WiddleWabbit/MQTT-ModularControllerBoard/Outputs/Models/MQTT-ModularControllerBoard-Back.png

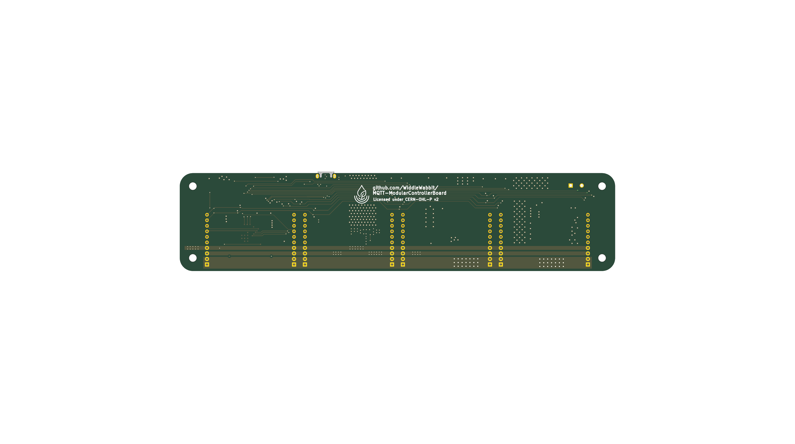
Outputs/Models/MQTT-ModularControllerBoard-Back.png
