WiddleWabbit/MQTT-ModularControllerBoard/Outputs/Models/MQTT-ModularControllerBoard-Front.png

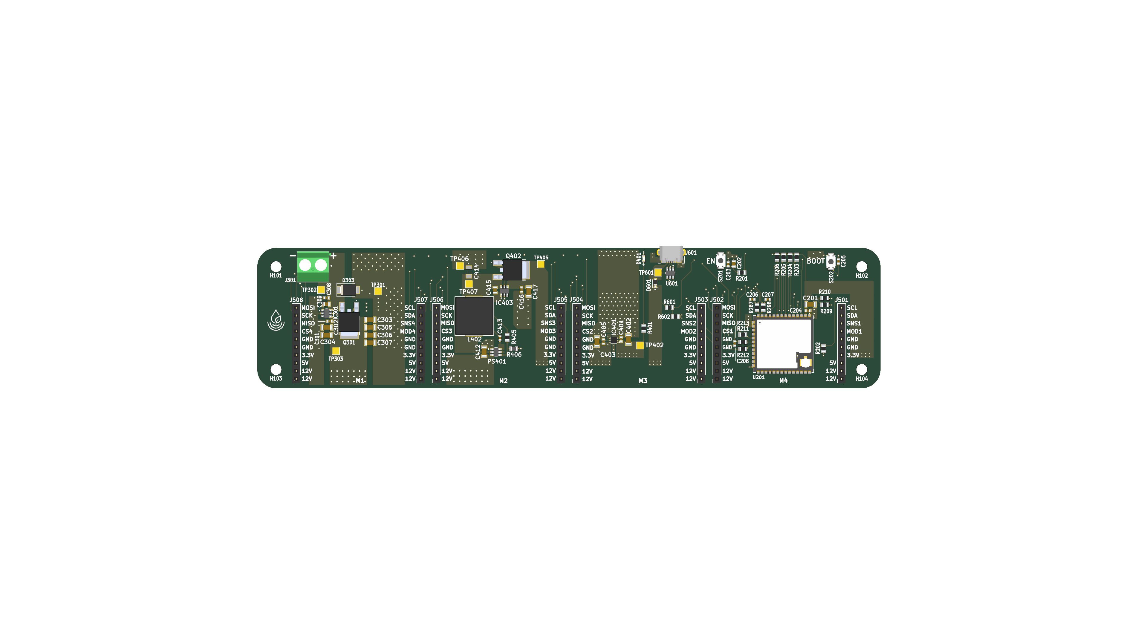
Outputs/Models/MQTT-ModularControllerBoard-Front.png
