WiddleWabbit/MQTT-ModularControllerBoard/Firmware/test/test_desktop/test_networking.cpp

#include <string>

#include <unity.h>

#include "MqttService.h"
#include "NtpService.h"
#include "WifiManager.h"
#include "fakes/FakeClock.h"
#include "fakes/FakeMqttClient.h"
#include "fakes/FakeNtpAdapter.h"
#include "fakes/FakeWifi.h"

namespace
{
FakeClock* clockForCallback = nullptr;
std::string receivedTopic;
std::string receivedPayload;

void recordMessage(const char* topic, const uint8_t* payload, size_t length,
                   void*)
{
  receivedTopic = topic == nullptr ? "" : topic;
  receivedPayload.assign(reinterpret_cast<const char*>(payload), length);
}

WifiManagerConfig wifiConfig()
{
  return {"garden", "secret", 1000, 100, 400};
}

MqttConfig mqttConfig()
{
  static const MqttSubscription subscriptions[] = {
    {"controller/command", 1},
    {"controller/config", 0},
  };
  return {"watering-controller", "user", "password", subscriptions, 2, 100, 400};
}
}

void setUp()
{
  clockForCallback = nullptr;
  receivedTopic.clear();
  receivedPayload.clear();
}

void tearDown()
{
}

void testWifiStartsConnectingAndReachesConnectedState()
{
  FakeClock clock;
  FakeWifi wifi;
  WifiManager manager(wifi, clock, wifiConfig());

  manager.begin();

  TEST_ASSERT_EQUAL(WifiManagerState::Connecting, manager.state());
  TEST_ASSERT_EQUAL(1, wifi.beginCallCount);
  TEST_ASSERT_EQUAL_STRING("garden", wifi.lastSsid.c_str());

  wifi.linkState = WifiLinkState::Connected;
  manager.update();

  TEST_ASSERT_EQUAL(WifiManagerState::Connected, manager.state());
  TEST_ASSERT_TRUE(manager.isConnected());
}

void testServicesRemainIdleUntilStarted()
{
  FakeClock clock;
  FakeWifi wifi;
  FakeNtpAdapter ntpAdapter;
  FakeMqttClient mqttClient;
  WifiManager wifiManager(wifi, clock, wifiConfig());
  NtpService ntpService(ntpAdapter, clock,
                        {"a", "b", "c", 0, 0, 100});
  MqttService mqttService(mqttClient, clock, mqttConfig());

  wifiManager.update();
  ntpService.update();
  mqttService.update(true);

  TEST_ASSERT_EQUAL(WifiManagerState::Idle, wifiManager.state());
  TEST_ASSERT_EQUAL(NtpServiceState::Idle, ntpService.state());
  TEST_ASSERT_EQUAL(MqttServiceState::Idle, mqttService.state());
  TEST_ASSERT_EQUAL(0, wifi.beginCallCount);
  TEST_ASSERT_EQUAL(0, ntpAdapter.configureCallCount);
  TEST_ASSERT_EQUAL(0, mqttClient.connectCallCount);
}

void testWifiTimeoutUsesBackoffWithoutBlocking()
{
  FakeClock clock;
  FakeWifi wifi;
  WifiManager manager(wifi, clock, wifiConfig());

  manager.begin();
  clock.advance(1000);
  manager.update();

  TEST_ASSERT_EQUAL(WifiManagerState::Backoff, manager.state());
  TEST_ASSERT_EQUAL(1, wifi.disconnectCallCount);
  TEST_ASSERT_EQUAL(1, wifi.beginCallCount);

  clock.advance(99);
  manager.update();
  TEST_ASSERT_EQUAL(1, wifi.beginCallCount);

  clock.advance(1);
  manager.update();
  TEST_ASSERT_EQUAL(WifiManagerState::Connecting, manager.state());
  TEST_ASSERT_EQUAL(2, wifi.beginCallCount);
}

void testWifiRetriesWithExponentialDelayAndCapsDelay()
{
  FakeClock clock;
  FakeWifi wifi;
  WifiManager manager(wifi, clock, wifiConfig());

  manager.begin();
  for (int attempt = 0; attempt < 3; ++attempt)
  {
    clock.advance(1000);
    manager.update();
    TEST_ASSERT_EQUAL(WifiManagerState::Backoff, manager.state());
    clock.advance(attempt == 0 ? 100 : (attempt == 1 ? 200 : 400));
    manager.update();
  }

  TEST_ASSERT_EQUAL(4, wifi.beginCallCount);
  TEST_ASSERT_EQUAL(400, manager.currentRetryDelayMs());
}

void testWifiReturnsToBackoffWhenConnectedLinkIsLost()
{
  FakeClock clock;
  FakeWifi wifi;
  WifiManager manager(wifi, clock, wifiConfig());

  manager.begin();
  wifi.linkState = WifiLinkState::Connected;
  manager.update();
  wifi.linkState = WifiLinkState::Disconnected;
  manager.update();

  TEST_ASSERT_EQUAL(WifiManagerState::Backoff, manager.state());
  TEST_ASSERT_FALSE(manager.isConnected());
}

void testWifiUsesStatusSequenceAndHandlesClockWraparound()
{
  FakeClock clock;
  clock.set(UINT32_MAX - 50U);
  FakeWifi wifi;
  wifi.statusSequence = {
    WifiLinkState::Connecting,
    WifiLinkState::Connected,
  };
  WifiManager manager(wifi, clock, wifiConfig());

  manager.begin();
  clock.advance(1000);
  manager.update();

  TEST_ASSERT_EQUAL(WifiManagerState::Backoff, manager.state());
  TEST_ASSERT_EQUAL(1, wifi.disconnectCallCount);

  clock.advance(101);
  manager.update();
  TEST_ASSERT_EQUAL(WifiManagerState::Connecting, manager.state());
  TEST_ASSERT_EQUAL(2, wifi.beginCallCount);

  manager.update();
  TEST_ASSERT_EQUAL(WifiManagerState::Connected, manager.state());
}

void testNtpConfiguresAdapterAndTransitionsWhenTimeIsValid()
{
  FakeClock clock;
  FakeNtpAdapter adapter;
  NtpService service(adapter, clock,
                     {"pool.ntp.org", "time.nist.gov", nullptr, 28800, 0, 500});

  service.begin();
  TEST_ASSERT_EQUAL(NtpServiceState::WaitingForSync, service.state());
  TEST_ASSERT_FALSE(service.isSynchronized());
  TEST_ASSERT_EQUAL((time_t)0, service.currentTime());
  TEST_ASSERT_EQUAL(1, adapter.configureCallCount);
  TEST_ASSERT_EQUAL(28800, adapter.lastUtcOffsetSeconds);

  service.update();
  TEST_ASSERT_EQUAL(NtpServiceState::WaitingForSync, service.state());

  adapter.synchronized = true;
  adapter.epoch = 1700000000;
  service.update();
  TEST_ASSERT_EQUAL(NtpServiceState::Synchronized, service.state());
  TEST_ASSERT_EQUAL((time_t)1700000000, service.currentTime());
}

void testNtpRetriesConfigurationAfterSyncWaitInterval()
{
  FakeClock clock;
  FakeNtpAdapter adapter;
  NtpService service(adapter, clock,
                     {"a", "b", "c", 0, 3600, 500});

  service.begin();
  clock.advance(499);
  service.update();
  TEST_ASSERT_EQUAL(1, adapter.configureCallCount);

  clock.advance(1);
  service.update();
  TEST_ASSERT_EQUAL(2, adapter.configureCallCount);
}

void testNtpReturnsToWaitingWhenSynchronizationIsLost()
{
  FakeClock clock;
  FakeNtpAdapter adapter;
  NtpService service(adapter, clock,
                     {"a", "b", "c", 0, 0, 100});

  service.begin();
  adapter.synchronized = true;
  adapter.epoch = 1700000001;
  service.update();
  TEST_ASSERT_EQUAL(NtpServiceState::Synchronized, service.state());

  adapter.synchronized = false;
  service.update();
  TEST_ASSERT_EQUAL(NtpServiceState::WaitingForSync, service.state());
  TEST_ASSERT_EQUAL((time_t)0, service.currentTime());

  clock.advance(100);
  service.update();
  TEST_ASSERT_EQUAL(2, adapter.configureCallCount);
}

void testMqttWaitsForNetworkThenConnectsAndSubscribes()
{
  FakeClock clock;
  FakeMqttClient client;
  MqttService service(client, clock, mqttConfig());

  service.setBroker("broker.local", 1883);
  service.begin();
  service.update(false);
  TEST_ASSERT_EQUAL(MqttServiceState::WaitingForNetwork, service.state());
  TEST_ASSERT_EQUAL(0, client.connectCallCount);

  service.update(true);
  TEST_ASSERT_EQUAL(MqttServiceState::Connected, service.state());
  TEST_ASSERT_EQUAL(1, client.connectCallCount);
  TEST_ASSERT_EQUAL(2, client.subscribeCallCount);
  TEST_ASSERT_EQUAL_STRING("controller/command",
                           client.subscribedTopics[0].c_str());
}

void testMqttFailedConnectionUsesNonblockingBackoff()
{
  FakeClock clock;
  FakeMqttClient client;
  client.connectResult = false;
  MqttService service(client, clock, mqttConfig());

  service.setBroker("broker.local", 1883);
  service.begin();
  service.update(true);
  TEST_ASSERT_EQUAL(MqttServiceState::Backoff, service.state());
  TEST_ASSERT_EQUAL(1, client.connectCallCount);

  clock.advance(99);
  service.update(true);
  TEST_ASSERT_EQUAL(1, client.connectCallCount);

  clock.advance(1);
  service.update(true);
  TEST_ASSERT_EQUAL(2, client.connectCallCount);
}

void testMqttServicesLoopAndPublishesOnlyWhenConnected()
{
  FakeClock clock;
  FakeMqttClient client;
  MqttService service(client, clock, mqttConfig());

  service.setBroker("broker.local", 1883);
  service.begin();
  TEST_ASSERT_FALSE(service.publish("status", "offline", false));
  service.update(true);
  TEST_ASSERT_TRUE(service.publish("status", "online", true));
  service.update(true);

  TEST_ASSERT_EQUAL(1, client.publishCallCount);
  TEST_ASSERT_EQUAL_STRING("online", client.publishedMessages[0].payload.c_str());
  TEST_ASSERT_EQUAL(1, client.loopCallCount);
}

void testMqttForwardsInboundMessagesToApplicationHandler()
{
  FakeClock clock;
  FakeMqttClient client;
  MqttService service(client, clock, mqttConfig());

  service.setMessageHandler(recordMessage, nullptr);
  service.setBroker("broker.local", 1883);
  service.begin();
  service.update(true);
  client.deliver("controller/command", "water-now");

  TEST_ASSERT_EQUAL_STRING("controller/command", receivedTopic.c_str());
  TEST_ASSERT_EQUAL_STRING("water-now", receivedPayload.c_str());
}

void testMqttDisconnectsWhenNetworkIsLost()
{
  FakeClock clock;
  FakeMqttClient client;
  MqttService service(client, clock, mqttConfig());

  service.setBroker("broker.local", 1883);
  service.begin();
  service.update(true);
  service.update(false);

  TEST_ASSERT_EQUAL(MqttServiceState::WaitingForNetwork, service.state());
  TEST_ASSERT_EQUAL(1, client.disconnectCallCount);
}

void testMqttRetriesAfterBrokerDisconnectUsingBackoff()
{
  FakeClock clock;
  FakeMqttClient client;
  MqttService service(client, clock, mqttConfig());

  service.setBroker("broker.local", 1883);
  service.begin();
  service.update(true);
  TEST_ASSERT_EQUAL(MqttServiceState::Connected, service.state());

  client.connectedState = false;
  service.update(true);
  TEST_ASSERT_EQUAL(MqttServiceState::Backoff, service.state());

  clock.advance(99);
  service.update(true);
  TEST_ASSERT_EQUAL(1, client.connectCallCount);

  clock.advance(1);
  service.update(true);
  TEST_ASSERT_EQUAL(2, client.connectCallCount);
  TEST_ASSERT_EQUAL(MqttServiceState::Connected, service.state());
}

void testMqttReportsPublicationFailure()
{
  FakeClock clock;
  FakeMqttClient client;
  client.publishResult = false;
  MqttService service(client, clock, mqttConfig());

  service.setBroker("broker.local", 1883);
  service.begin();
  service.update(true);

  TEST_ASSERT_FALSE(service.publish("status", "online", false));
  TEST_ASSERT_EQUAL(1, client.publishCallCount);
}

void testMqttBacksOffWhenSubscriptionFails()
{
  FakeClock clock;
  FakeMqttClient client;
  client.subscribeResults = {true, false};
  MqttService service(client, clock, mqttConfig());

  service.setBroker("broker.local", 1883);
  service.begin();
  service.update(true);

  TEST_ASSERT_EQUAL(MqttServiceState::Backoff, service.state());
  TEST_ASSERT_EQUAL(1, client.disconnectCallCount);
  TEST_ASSERT_FALSE(service.publish("status", "online", false));
}

void testWifiAndMqttComposeThroughInterfaces()
{
  FakeClock clock;
  FakeWifi wifi;
  FakeMqttClient client;
  WifiManager manager(wifi, clock, wifiConfig());
  MqttService mqtt(client, clock, mqttConfig());

  manager.begin();
  mqtt.setBroker("broker.local", 1883);
  mqtt.begin();
  mqtt.update(manager.isConnected());
  TEST_ASSERT_EQUAL(0, client.connectCallCount);

  wifi.linkState = WifiLinkState::Connected;
  manager.update();
  mqtt.update(manager.isConnected());

  TEST_ASSERT_EQUAL(1, client.connectCallCount);
  TEST_ASSERT_EQUAL(MqttServiceState::Connected, mqtt.state());
}

void testMqttWithoutBrokerStaysUnconfigured()
{
  FakeClock clock;
  FakeMqttClient client;
  MqttService service(client, clock, mqttConfig());

  service.setBroker("", 1883);
  service.begin();
  service.update(true);
  service.update(true);

  TEST_ASSERT_EQUAL(MqttServiceState::Unconfigured, service.state());
  TEST_ASSERT_EQUAL(0, client.connectCallCount);

  service.setBroker(nullptr, 1883);
  service.update(true);
  TEST_ASSERT_EQUAL(0, client.connectCallCount);

  service.setBroker("broker.local", 1883);
  service.begin();
  service.update(true);

  TEST_ASSERT_EQUAL(1, client.connectCallCount);
  TEST_ASSERT_EQUAL(MqttServiceState::Connected, service.state());
}


// ========== Runner ==========

/**
 * Registers the Wi-Fi, NTP, and MQTT service cases.
 *
 * @return Nothing.
 */
void runNetworkingTests()
{
  // UNITY_BEGIN records test_main.cpp, so name this file for the report.
  UnitySetTestFile(__FILE__);
  RUN_TEST(testWifiStartsConnectingAndReachesConnectedState);
  RUN_TEST(testServicesRemainIdleUntilStarted);
  RUN_TEST(testWifiTimeoutUsesBackoffWithoutBlocking);
  RUN_TEST(testWifiRetriesWithExponentialDelayAndCapsDelay);
  RUN_TEST(testWifiReturnsToBackoffWhenConnectedLinkIsLost);
  RUN_TEST(testWifiUsesStatusSequenceAndHandlesClockWraparound);
  RUN_TEST(testNtpConfiguresAdapterAndTransitionsWhenTimeIsValid);
  RUN_TEST(testNtpRetriesConfigurationAfterSyncWaitInterval);
  RUN_TEST(testNtpReturnsToWaitingWhenSynchronizationIsLost);
  RUN_TEST(testMqttWaitsForNetworkThenConnectsAndSubscribes);
  RUN_TEST(testMqttFailedConnectionUsesNonblockingBackoff);
  RUN_TEST(testMqttServicesLoopAndPublishesOnlyWhenConnected);
  RUN_TEST(testMqttForwardsInboundMessagesToApplicationHandler);
  RUN_TEST(testMqttDisconnectsWhenNetworkIsLost);
  RUN_TEST(testMqttRetriesAfterBrokerDisconnectUsingBackoff);
  RUN_TEST(testMqttReportsPublicationFailure);
  RUN_TEST(testMqttBacksOffWhenSubscriptionFails);
  RUN_TEST(testWifiAndMqttComposeThroughInterfaces);
  RUN_TEST(testMqttWithoutBrokerStaysUnconfigured);
}
